cookiemonsternz/Eurorack-DIST/hardware/ltspice/od.asc

B1: bv; V=V(VIN)*5
B2: bv; V=V(VOUT)/5
C2: cap; 22n
C3: cap; 1n
C4: cap; 220n
C5: cap; 220n
C6: cap; 220n
C7: cap; 1n
C8: cap; 1n
D1: diode; 1N4148
D2: diode; 1N4148
R4: res; 1Meg
R5: res; 10k
R6: res; 1k
R7: res; 1k
R8: res; 560
R9: res; 2.2k
R10: res; 220k
R11: res; 5k
R12: res; 5k
R13: res; 1k
R14: res; 220k
R15: res; 10k
R16: res; 90k
R17: res; 200k
R18: res; 100k
R19: res; 40k
R20: res; 10k
U1: opamp2; TL072
U2: opamp2; TL072
U3: opamp2; TL072
V1: voltage; SINE(0 1 {freq})
V2: voltage; PULSE(0 250m 0 {0.5/freq} {0.5/freq} 0 {1/freq})
V3: voltage; 12
V4: voltage; wavefile="C:\input.wav" chan=0
V5: voltage; -12
Named nets: VIN, IN, VSS, VDD, VOUT, OUT, 0
.tran 5
.SUBCKT TL072    1 2 3 4 5
*
  C1   11 12 3.498E-12
  C2    6  7 15.00E-12
  DC    5 53 DX
  DE   54  5 DX
  DLP  90 91 DX
  DLN  92 90 DX
  DP    4  3 DX
  EGND 99  0 POLY(2) (3,0) (4,0) 0 .5 .5
  FB    7 99 POLY(5) VB VC VE VLP VLN 0 4.715E6 -5E6 5E6 5E6 -5E6
  GA    6  0 11 12 282.8E-6
  GCM   0  6 10 99 8.942E-9
  ISS   3 10 DC 195.0E-6
  HLIM 90  0 VLIM 1K
  J1   11  2 10 JX
  J2   12  1 10 JX
  R2    6  9 100.0E3
  RD1   4 11 3.536E3
  RD2   4 12 3.536E3
  RO1   8  5 150
  RO2   7 99 150
  RP    3  4 2.143E3
  RSS  10 99 1.026E6
  VB    9  0 DC 0
  VC    3 53 DC 2.200
  VE   54  4 DC 2.200
  VLIM  7  8 DC 0
  VLP  91  0 DC 25
  VLN   0 92 DC 25
.MODEL DX D(IS=800.0E-18)
.MODEL JX PJF(IS=15.00E-12 BETA=270.1E-6 VTO=-1)
.ENDS
.param freq=100
.wave "C:\\export.wav" 16 44.1k V(OUT)
SINE
TRI
AUDIO
SOURCES
POWER
TONE POT
VOL POT
SCALE TO +-5V
SCALE TO +-1V
INPUT SCALING
CLIPPING
TONE
OUTPUT SCALING
