cookiemonsternz/Eurorack-DIST/hardware/ltspice/fuzz.asc

B1: bv; V=V(VIN)*5
B2: bv; V=V(VOUT)/8
C3: cap; 22n
C4: cap; 1µ
C5: cap; 100n
C6: cap; 1n
C7: polcap; 1µ
C8: cap; 100n
C9: cap; 1n
C10: polcap; 1µ
C11: cap; 4n
C12: cap; 10n
C13: cap; 220n
C14: cap; 22n
D1: diode; 1N4148
D2: diode; 1N4148
D3: diode; 1N4148
D4: diode; 1N4148
Q1: npn; BC547B
Q2: npn; BC547B
R4: res; 200k
R5: res; 100k
R7: res; 6.8k
R8: res; 100k
R9: res; 10k
R10: res; 50k
R11: res; 50k
R12: res; 1k
R13: res; 10k
R14: res; 100k
R15: res; 150
R16: res; 470k
R17: res; 10k
R18: res; 10k
R19: res; 100k
R20: res; 150
R21: res; 470k
R22: res; 10k
R23: res; 39k
R24: res; 50k
R25: res; 50k
R26: res; 22k
R27: res; 150k
R28: res; 10k
R29: res; 10k
R30: res; 90k
R31: res; 560
R32: res; 1Meg
U1: opamp2; TL072
U2: opamp2; TL072
V1: voltage; PULSE(0 250m 0 {0.5/freq} {0.5/freq} 0 {1/freq})
V2: voltage; 12
V3: voltage; SINE(0 1 {freq})
V4: voltage; wavefile="C:\input.wav" chan=0
V5: voltage; -12
Named nets: VIN, IN, OUT, VSS, VDD, VOUT, 0
.param freq=100
SINE
TRI
AUDIO
SOURCES
POWER
SCALE TO +-5V
SCALE TO +-1V
.tran 5
.wave "C:\\export.wav" 16 44.1k V(OUT)
INPUT FILTERING
SCALE
DRIVE POT
100k-A
SUSTAIN | DRIVE
CLIP A
.SUBCKT TL072    1 2 3 4 5
*
  C1   11 12 3.498E-12
  C2    6  7 15.00E-12
  DC    5 53 DX
  DE   54  5 DX
  DLP  90 91 DX
  DLN  92 90 DX
  DP    4  3 DX
  EGND 99  0 POLY(2) (3,0) (4,0) 0 .5 .5
  FB    7 99 POLY(5) VB VC VE VLP VLN 0 4.715E6 -5E6 5E6 5E6 -5E6
  GA    6  0 11 12 282.8E-6
  GCM   0  6 10 99 8.942E-9
  ISS   3 10 DC 195.0E-6
  HLIM 90  0 VLIM 1K
  J1   11  2 10 JX
  J2   12  1 10 JX
  R2    6  9 100.0E3
  RD1   4 11 3.536E3
  RD2   4 12 3.536E3
  RO1   8  5 150
  RO2   7 99 150
  RP    3  4 2.143E3
  RSS  10 99 1.026E6
  VB    9  0 DC 0
  VC    3 53 DC 2.200
  VE   54  4 DC 2.200
  VLIM  7  8 DC 0
  VLP  91  0 DC 25
  VLN   0 92 DC 25
.MODEL DX D(IS=800.0E-18)
.MODEL JX PJF(IS=15.00E-12 BETA=270.1E-6 VTO=-1)
.ENDS
CLIP B
TONE
VOL POT
100k-A
VOLUME
