cookiemonsternz/Eurorack-DIST/hardware/ltspice/structure.asc

C1: polcap; 47µ
C2: cap; 22n
C3: cap; 220n
C4: cap; 22n
C5: cap; 220n
C6: cap; 220n
C7: cap; 220n
C8: cap; 22n
C9: cap; 22n
R1: res; 100k
R2: res; 100k
R3: res; 47
R4: res; 1Meg
R5: res; 100k
R6: res; 1Meg
R7: res; 100k
R8: res; 100k
R9: res; 100k
R10: res; 1Meg
R11: res; 1Meg
R12: res; 50k
R13: res; 50k
U1: opamp2; TL072
U2: opamp2; TL072
U3: opamp2; TL072
U4: opamp2; TL072
U5: opamp2; TL072
U6: opamp2; TL072
U7: opamp2; TL072
U8: opamp2; TL072
V2: voltage; 24
Named nets: BIAS, VSS, VDD, 0, OD_IN, OD_OUT, DIST_OUT, FUZZ_OUT, WRMERGLE_OUT, DIST_IN, FUZZ_IN, WRMERGLE_IN
POWER
OD
DIST
FUZZ
WRMERGLE
BIAS
BIAS
BIAS
BIAS
BIAS
BIAS
BIAS
BIAS
FEEDBACK
A-100k
