cookiemonsternz/Eurorack-DIST/hardware/ltspice/gate.asc

B1: bv; V=V(VIN)*1
B2: bv; V=V(VOUT)/8
C1: polcap; 47µ
C2: polcap; 10µ
C3: polcap; 4.7µ
C4: cap; 220n
C5: polcap; 10n
C6: polcap; 10n
D1: diode; 1N4148
D2: diode; 1N4148
M1: nmos; BSP89
Q1: npn; BC547B
Q2: npn; BC547B
R1: res; 10k
R2: res; 10k
R3: res; 47
R4: res; 2.2k
R5: res; 1k
R6: res; 470k
R7: res; 2.2Meg
R8: res; 4.7k
R9: res; 50k
R10: res; 5k
R11: res; 220
U1: opamp2; TL072
V1: voltage; PULSE(0 250m 0 {0.5/freq} {0.5/freq} 0 {1/freq})
V2: voltage; 9
V3: voltage; SINE(0 1 {freq})
V4: voltage; wavefile="C:\input.wav" chan=0
V5: voltage; wavefile="C:\input2.wav" chan=0
Named nets: VSS, BIAS, VDD, 0, VIN, IN, OUT, VOUT
.param freq=100
SINE
TRI
AUDIO
SOURCES
POWER
SCALE TO +-5V
SCALE TO +-1V
.tran 5
.wave "C:\\export.wav" 16 44.1k V(OUT)
GATE POT
100k-B
.SUBCKT TL072    1 2 3 4 5
*
  C1   11 12 3.498E-12
  C2    6  7 15.00E-12
  DC    5 53 DX
  DE   54  5 DX
  DLP  90 91 DX
  DLN  92 90 DX
  DP    4  3 DX
  EGND 99  0 POLY(2) (3,0) (4,0) 0 .5 .5
  FB    7 99 POLY(5) VB VC VE VLP VLN 0 4.715E6 -5E6 5E6 5E6 -5E6
  GA    6  0 11 12 282.8E-6
  GCM   0  6 10 99 8.942E-9
  ISS   3 10 DC 195.0E-6
  HLIM 90  0 VLIM 1K
  J1   11  2 10 JX
  J2   12  1 10 JX
  R2    6  9 100.0E3
  RD1   4 11 3.536E3
  RD2   4 12 3.536E3
  RO1   8  5 150
  RO2   7 99 150
  RP    3  4 2.143E3
  RSS  10 99 1.026E6
  VB    9  0 DC 0
  VC    3 53 DC 2.200
  VE   54  4 DC 2.200
  VLIM  7  8 DC 0
  VLP  91  0 DC 25
  VLN   0 92 DC 25
.MODEL DX D(IS=800.0E-18)
.MODEL JX PJF(IS=15.00E-12 BETA=270.1E-6 VTO=-1)
.ENDS
